lluki/party-teddy/sketch_teddy/AudioOutputI2SNoDACBeatDetect.cpp

/*
  AudioOutputI2SNoDAC
  Audio player using SW delta-sigma to generate "analog" on I2S data
 
  Copyright (C) 2017  Earle F. Philhower, III

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
  You should have received a copy of the GNU General Public License
  along with this program.  If not, see <http://www.gnu.org/licenses/>.
*/

#include <Arduino.h>
#include "dft.h"

#ifdef ESP32
  #include "driver/i2s.h"
#else
  #include <i2s.h>
#endif
#include "AudioOutputI2SNoDACBeatDetect.h"

static inline int32_t asm_ccount(void) {
    int32_t r;
    asm volatile ("rsr %0, ccount" : "=r"(r));
    return r;
}

AudioOutputI2SNoDACBeatDetect::AudioOutputI2SNoDACBeatDetect(LED_ON led_on_callback,float power_th, int port)
    : AudioOutputI2SNoDAC(port)
    
{
    this->callback = led_on_callback;
    this->power_th = power_th;
    dft_reset();
}

AudioOutputI2SNoDACBeatDetect::~AudioOutputI2SNoDACBeatDetect()
{
}

bool AudioOutputI2SNoDACBeatDetect::ConsumeSample(int16_t sample[2])
{ 
  bool res = AudioOutputI2SNoDAC::ConsumeSample(sample);

  MakeSampleStereo16( sample );
  dft_new_sample(sample[0]);
  if(dft_ready()){
    float res = dft_read_res();
    if(res > this->power_th) this->callback(true);
    else this->callback(false);
    dft_reset();
  }
  return res;
}
